rotorman/USB2PPM/PIC32_firmware/firmware/src/app.h

/*******************************************************************************
  MPLAB Harmony Application Header File

  Company:
    Microchip Technology Inc.

  File Name:
    app.h

  Summary:
    This header file provides prototypes and definitions for the application.

  Description:
    This header file provides function prototypes and data type definitions for
    the application.  Some of these are required by the system (such as the
    "APP_Initialize" and "APP_Tasks" prototypes) and some of them are only used
    internally by the application (such as the "APP_STATES" definition).  Both
    are defined here for convenience.
*******************************************************************************/

//DOM-IGNORE-BEGIN
/*******************************************************************************
Copyright (c) 2013-2014 released Microchip Technology Inc.  All rights reserved.

Microchip licenses to you the right to use, modify, copy and distribute
Software only when embedded on a Microchip microcontroller or digital signal
controller that is integrated into your product or third party product
(pursuant to the sublicense terms in the accompanying license agreement).

You should refer to the license agreement accompanying this Software for
additional information regarding your rights and obligations.

SOFTWARE AND DOCUMENTATION ARE PROVIDED "AS IS" WITHOUT WARRANTY OF ANY KIND,
EITHER EXPRESS OR IMPLIED, INCLUDING WITHOUT LIMITATION, ANY WARRANTY OF
MERCHANTABILITY, TITLE, NON-INFRINGEMENT AND FITNESS FOR A PARTICULAR PURPOSE.
IN NO EVENT SHALL MICROCHIP OR ITS LICENSORS BE LIABLE OR OBLIGATED UNDER
CONTRACT, NEGLIGENCE, STRICT LIABILITY, CONTRIBUTION, BREACH OF WARRANTY, OR
OTHER LEGAL EQUITABLE THEORY ANY DIRECT OR INDIRECT DAMAGES OR EXPENSES
INCLUDING BUT NOT LIMITED TO ANY INCIDENTAL, SPECIAL, INDIRECT, PUNITIVE OR
CONSEQUENTIAL DAMAGES, LOST PROFITS OR LOST DATA, COST OF PROCUREMENT OF
SUBSTITUTE GOODS, TECHNOLOGY, SERVICES, OR ANY CLAIMS BY THIRD PARTIES
(INCLUDING BUT NOT LIMITED TO ANY DEFENSE THEREOF), OR OTHER SIMILAR COSTS.
 *******************************************************************************/
//DOM-IGNORE-END

#ifndef _APP_H
#define _APP_H

//#define FREERTOSSTATISTICS

// *****************************************************************************
// *****************************************************************************
// Section: Included Files
// *****************************************************************************
// *****************************************************************************

#include <stdint.h>
#include <stdbool.h>
#include <stddef.h>
#include <stdlib.h>
#include "system_config.h"
#include "system_definitions.h"
#include "USBCDC.h"

// *****************************************************************************
// *****************************************************************************
// Section: Type Definitions
// *****************************************************************************
// *****************************************************************************

// *****************************************************************************
// *****************************************************************************
// Section: Configuration specific application constants
// *****************************************************************************
// *****************************************************************************


#define LOWPULSEDURATIONUS              400     // Low pulse should be 400µs long
#define DEFAULTSERVOPOSITIONUS          1500    // Default servo position 1500µs
#define MINSERVOPOSITIONUS              1000    // 1 ms
#define MAXSERVOPOSITIONUS              2000    // 2 ms
#define FRAMELENGTHUS                   20000   // 20 ms frame length
#define FIXCOMPAREMISSINGTICK           1       // hardware compare module needs an extra clock cycle
#define CHANNELCOUNT                    8       // handle 8 servo channels
#define HEADERCOUNT                     2
#define HEADER1                         0xF0
#define HEADER2                         0xC4
#define BYTESPERCHANNEL                 2       // uint16
#define TMRTICKSPERUS                   5       // 5 Ticks per 1 µs, 200 ns resolution

typedef enum
{
	/* Application's state machine's initial state. */
    APP_STATE_REGISTER_TIMER_ALARM=0,
    APP_STATE_START_PULSE_OUTPUT,
    APP_STATE_GATHER_SAMPLES,
} APP_STATES;

typedef struct
{
    uint16_t ui16_ServoPulseDurationTMRticks[CHANNELCOUNT];
} SERVO_POSITIONS_TYPE;

// *****************************************************************************
/* Application Data

  Summary:
    Holds application data

  Description:
    This structure holds the application's data.

  Remarks:
    Application strings and buffers are be defined outside this structure.
 */

typedef struct
{
    DRV_HANDLE  CAPTURECOMPARE_timer_handle;

    /* The application's current state */
    APP_STATES state;
    
    TaskHandle_t th_APP_Tasks;
#ifdef FREERTOSSTATISTICS
    UBaseType_t AppStackHighWaterMark;
#endif
} APP_DATA;

// *****************************************************************************
// *****************************************************************************
// Section: Application Initialization and State Machine Functions
// *****************************************************************************
// *****************************************************************************

/*******************************************************************************
  Function:
    void APP_Initialize ( void )

  Summary:
     MPLAB Harmony application initialization routine.

  Description:
    This function initializes the Harmony application.  It places the 
    application in its initial state and prepares it to run so that its 
    APP_Tasks function can be called.

  Precondition:
    All other system initialization routines should be called before calling
    this routine (in "SYS_Initialize").

  Parameters:
    None.

  Returns:
    None.

  Example:
    <code>
    APP_Initialize();
    </code>

  Remarks:
    This routine must be called from the SYS_Initialize function.
*/

void APP_Initialize ( void );


/*******************************************************************************
  Function:
    void APP_Tasks ( void )

  Summary:
    MPLAB Harmony Demo application tasks function

  Description:
    This routine is the Harmony Demo application's tasks function.  It
    defines the application's state machine and core logic.

  Precondition:
    The system and application initialization ("SYS_Initialize") should be
    called before calling this.

  Parameters:
    None.

  Returns:
    None.

  Example:
    <code>
    APP_Tasks();
    </code>

  Remarks:
    This routine must be called from SYS_Tasks() routine.
 */

void APP_Tasks ( void );


#endif /* _APP_H */
/*******************************************************************************
 End of File
 */
